jwestfall69/openkey-cps2/images/board_panel.jpg

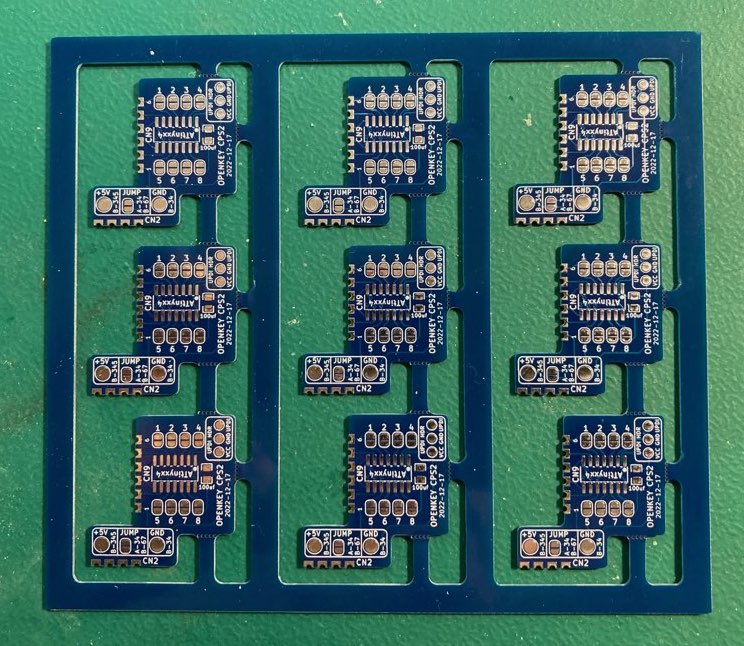
images/board_panel.jpg
