jwestfall69/openkey-cps2/images/identify_board1.jpg

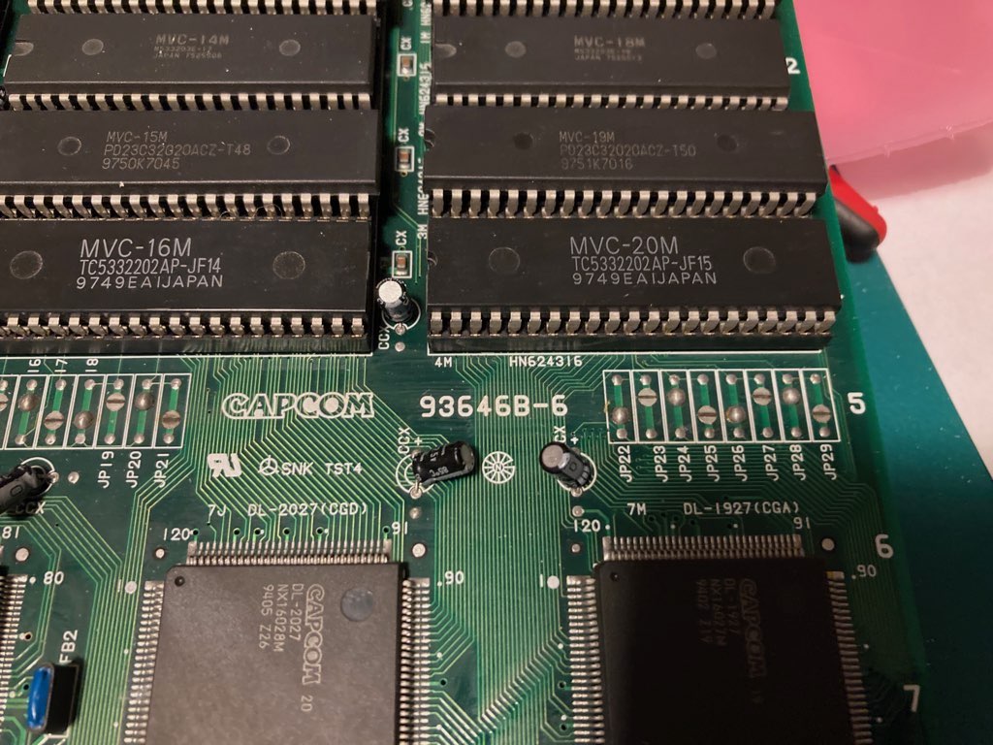
images/identify_board1.jpg
