jwestfall69/openkey-cps2/images/identify_board2.jpg

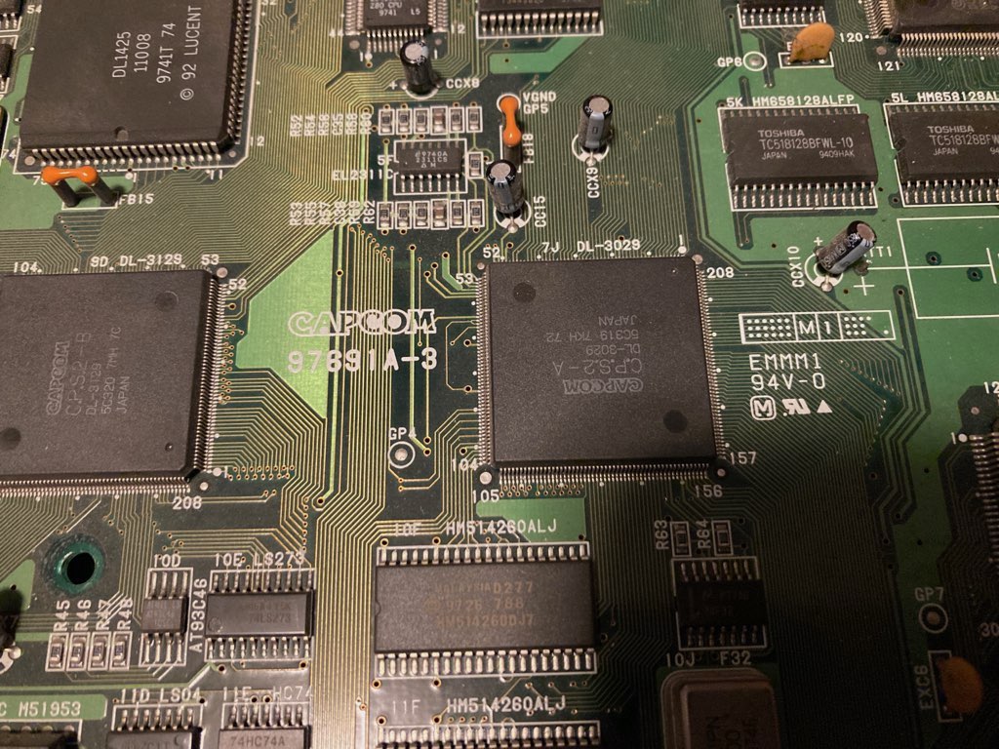
images/identify_board2.jpg
